ashllay/romprogrammer/firmware/bits.h

#pragma once

#define set(port, bit, onoff) do { (port) = ((port) & ~(1<<(bit))) | ((onoff) << (bit)); } while(0)
#define sbi(port, bit) do { (port) = (port) | (1<<(bit)); } while(0)
#define cbi(port, bit) do { (port) = (port) & ~(1<<(bit)); } while(0)
#define trigger(port, bit) do { sbi(port, bit); cbi(port, bit); } while(0)
